Wriju-Mitra/Opto-Hood/Images/IMG_20240819_154223.jpg

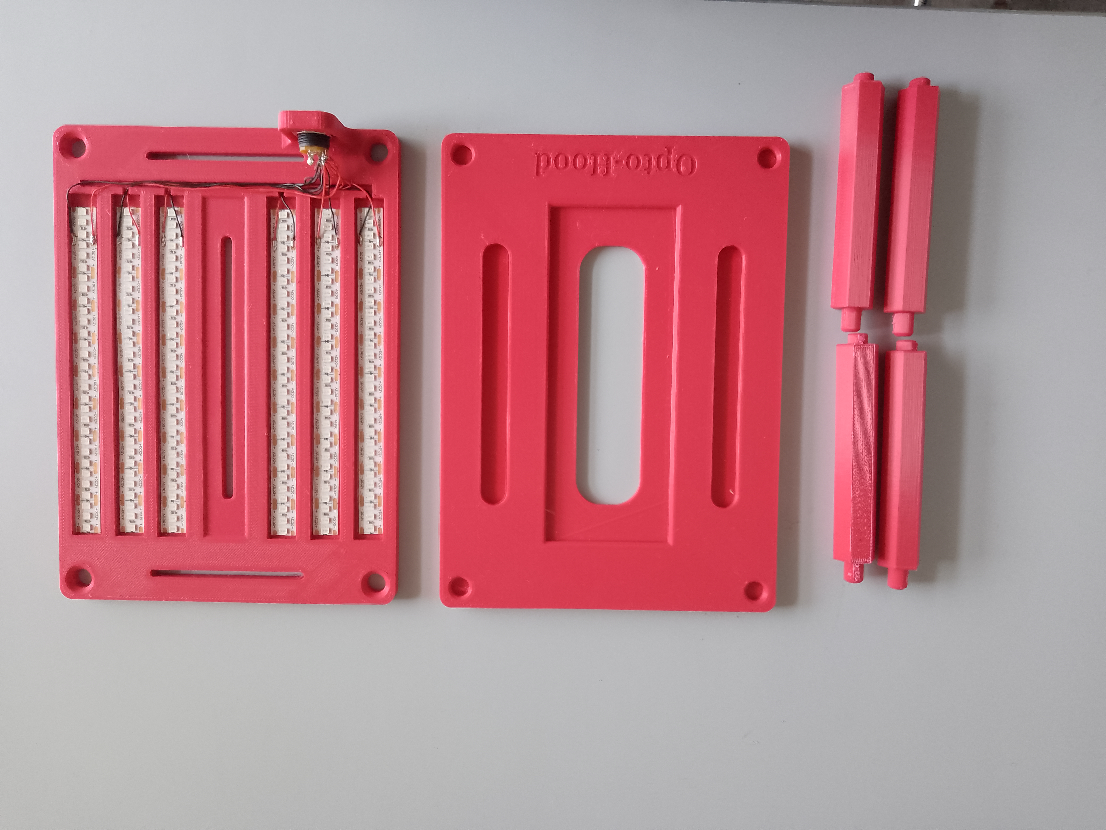
Images/IMG_20240819_154223.jpg
