Wriju-Mitra/Opto-Hood/Images/IMG_20240826_180829.jpg

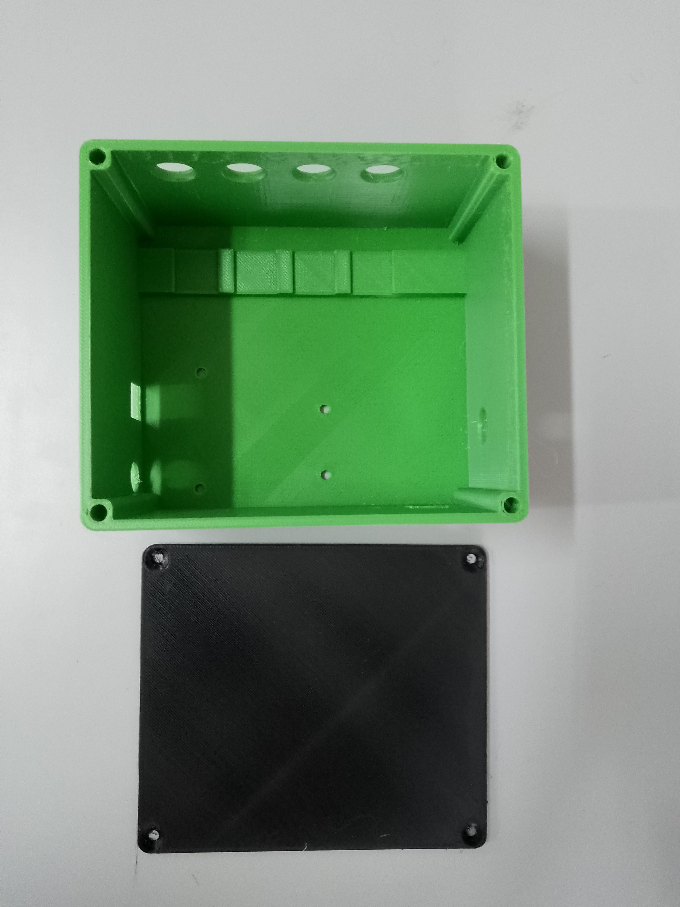
Images/IMG_20240826_180829.jpg
