Wriju-Mitra/Opto-Hood/Images/IMG_20240827_194018.jpg

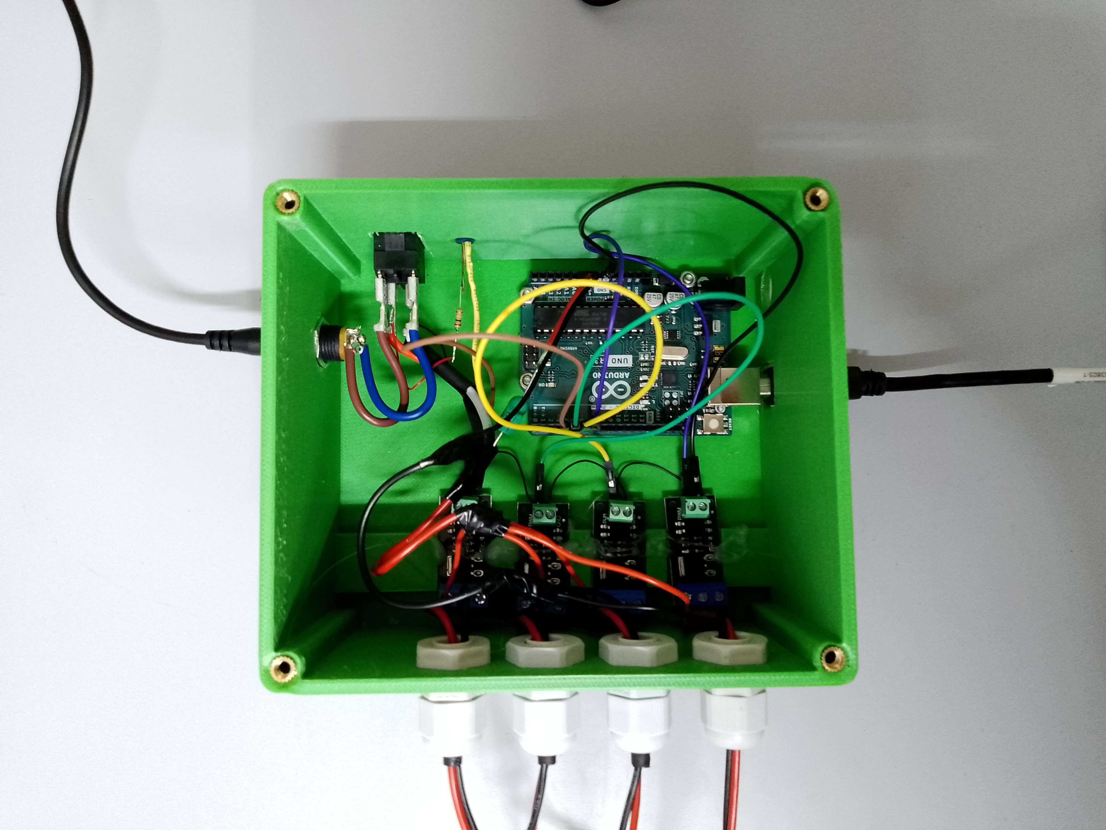
Images/IMG_20240827_194018.jpg
