Wriju-Mitra/Opto-Hood/Images/IMG_20240908_163527.jpg

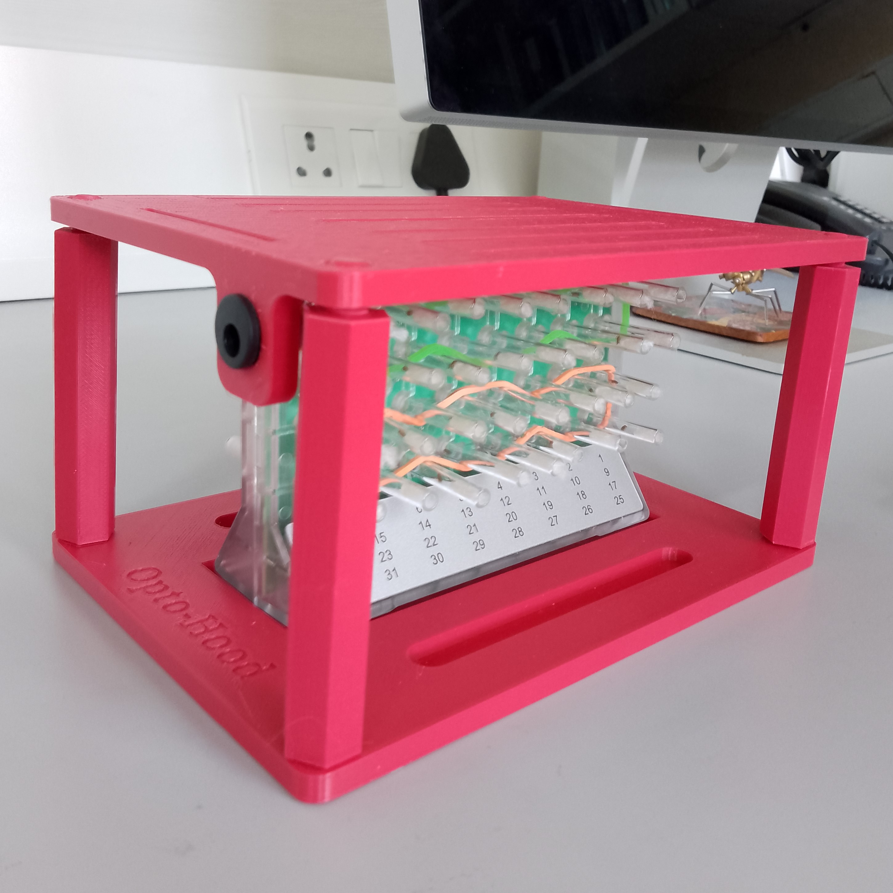
Images/IMG_20240908_163527.jpg
